gurul/spotify-knob/case/export/base_iso.png

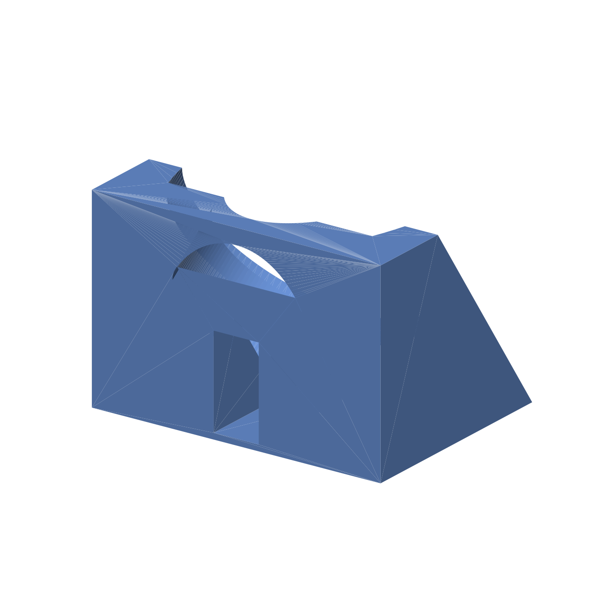
case/export/base_iso.png
