gurul/spotify-knob/case/export/base_section.png

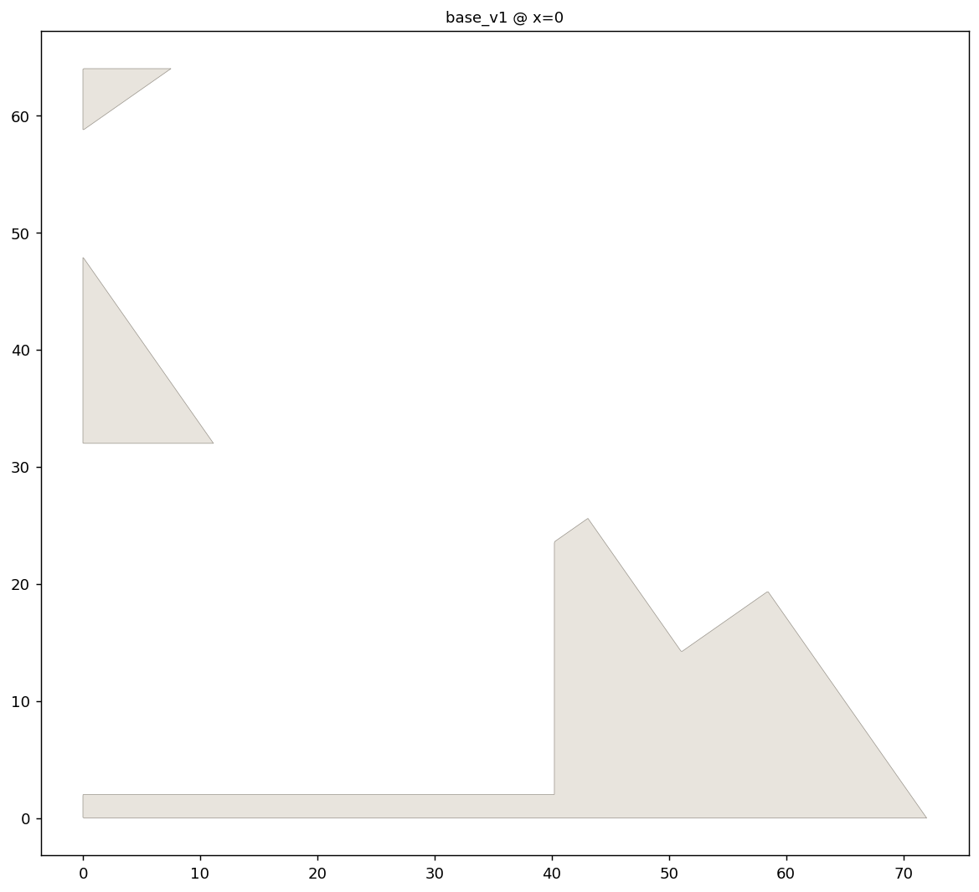
case/export/base_section.png
