gurul/spotify-knob/case/export/gauge_section.png

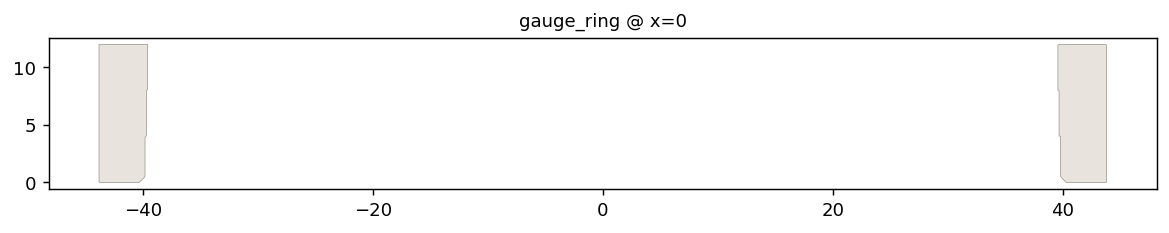
case/export/gauge_section.png
