gurul/spotify-knob/src/Board/Touch.h

/*-------------------------------------------------------------------------------------------------
**
** Touch.h
**
**    CST8xx capacitive touch for the CrowPanel 2.1" rotary display.
**
**    The controller's reset and interrupt lines are on the PCF8574 (P0 and P2),
**    not GPIO, so the reset pulse has to go over I2C before the controller will
**    answer on 0x15. This class also raises the raw stream to the gestures the
**    round UI needs: tap, and horizontal swipe for track skip.
**
** SPDX-License-Identifier: MIT
** ------------------------------------------------------------------------------------------------
*/

#pragma once

#include <Adafruit_CST8XX.h>
#include <Arduino.h>

#include "BoardPins.h"

/// Source-compatible replacement for FT6236.h's TS_Point.
///
/// The UIViews take TS_Point by reference, so keeping the name lets them port
/// untouched. FT6236 itself is not built — it is an I2C driver for a different
/// controller and would fight the CST8xx on the same bus.
class TS_Point {
public:
  TS_Point() : x(0), y(0), z(0) {}
  TS_Point(int16_t px, int16_t py, int16_t pz = 0) : x(px), y(py), z(pz) {}

  bool operator==(TS_Point o) { return x == o.x && y == o.y && z == o.z; }
  bool operator!=(TS_Point o) { return !(*this == o); }

  int16_t x;
  int16_t y;
  int16_t z;
};

enum class TouchGesture : uint8_t {
  None,
  Tap,
  SwipeLeft,
  SwipeRight,
  SwipeUp,
  SwipeDown,
};

struct TouchEvent {
  TouchGesture gesture = TouchGesture::None;
  int16_t      x       = 0;   ///< position where the gesture started
  int16_t      y       = 0;
};

class Touch {
public:
  /// Resets the controller through the expander, then probes it on I2C.
  bool begin();

  /// True while a finger is down; fills x/y with the current point.
  bool raw(int16_t &x, int16_t &y);

  /// Drains one recognized gesture. Returns false when nothing completed.
  bool poll(TouchEvent &out);

  bool present() const { return _present; }

private:
  /// A drag shorter than this is a tap, not a swipe.
  static constexpr int16_t  SWIPE_MIN_PX  = 60;
  /// Held longer than this without moving, it is neither.
  static constexpr uint32_t GESTURE_MAX_MS = 900;

  Adafruit_CST8XX _ts;
  bool            _present   = false;

  bool     _down     = false;
  int16_t  _startX   = 0;
  int16_t  _startY   = 0;
  int16_t  _lastX    = 0;
  int16_t  _lastY    = 0;
  uint32_t _startMs  = 0;
};

extern Touch touch;
